essensys-hub/essensys-raspberry-gateway/docs/client-android.md

# Client Android

L'application Android officielle pour le système Essensys.

## Téléchargement

Vous pouvez télécharger la dernière version de l'application (APK) directement ici :

[:material-android: Télécharger Essensys Android v1.0.0](https://github.com/essensys-hub/essensys-android-phone-apps/raw/refs/heads/main/mon.essensys.v.1.0.0.apk){ .md-button .md-button--primary }

## Aperçu

Voici quelques captures d'écran de l'application :

### Accueil et Navigation
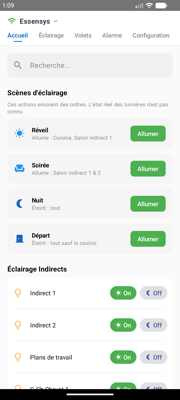
[picture p3: docs/img/app_android_001.png]
Accueil


### Éclairage
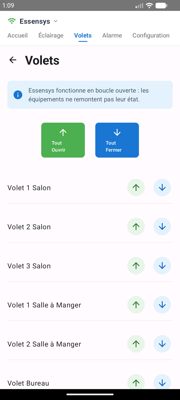
[picture p4: docs/img/app_android_002.png]
Éclairage

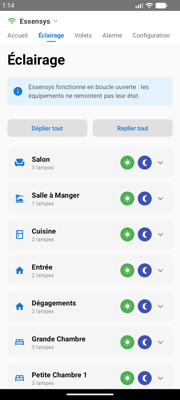
[picture p5: docs/img/app_android_003.png]
Contrôle Éclairage


### Volets
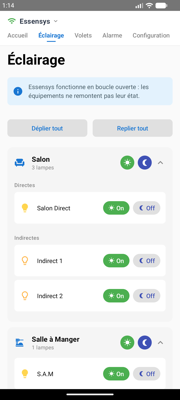
[picture p6: docs/img/app_android_004.png]
Volets


### Configuration
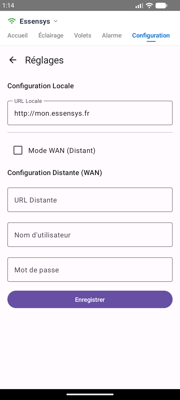
[picture p7: docs/img/app_android_005.png]
Configuration
